AdvaitThale/Solar-MPPT/Final Review/5v-3010-cooling-fan-for-raspberry-pi-550x550.webp

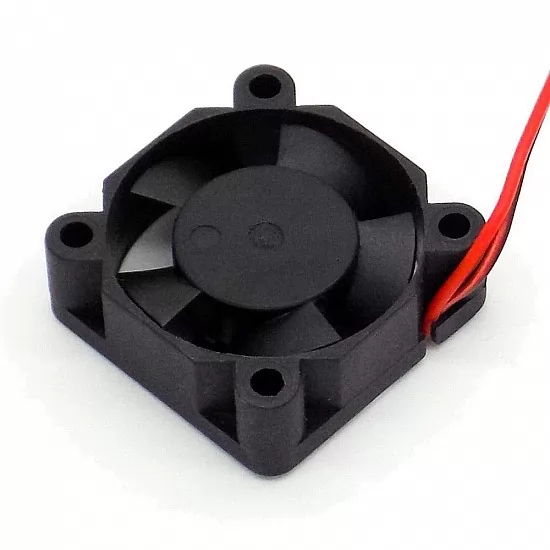
Final Review/5v-3010-cooling-fan-for-raspberry-pi-550x550.webp
