AdvaitThale/Solar-MPPT/Final Review/Back view.png

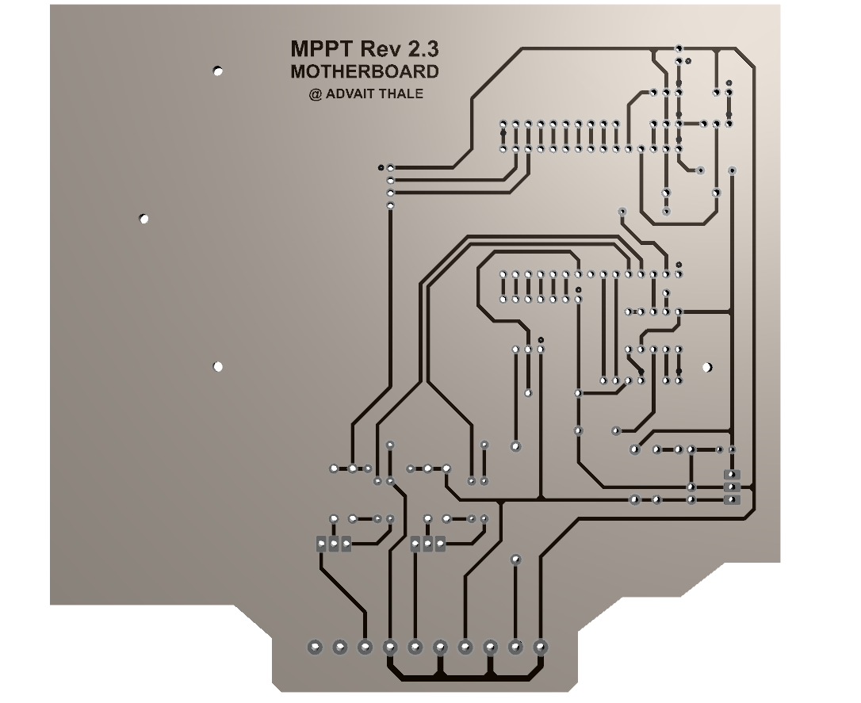
Final Review/Back view.png
