AdvaitThale/Solar-MPPT/Final Review/ESP32-LED-Blink.jpg

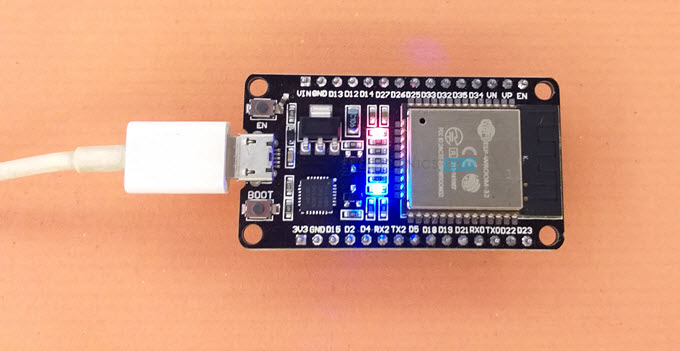
Final Review/ESP32-LED-Blink.jpg
