AdvaitThale/Solar-MPPT/Final Review/inv dau.PNG

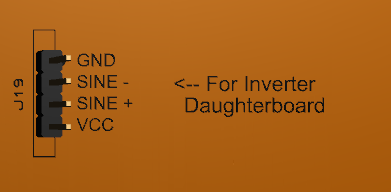
Final Review/inv dau.PNG
