AdvaitThale/Solar-MPPT/Final Review/Main B.PNG

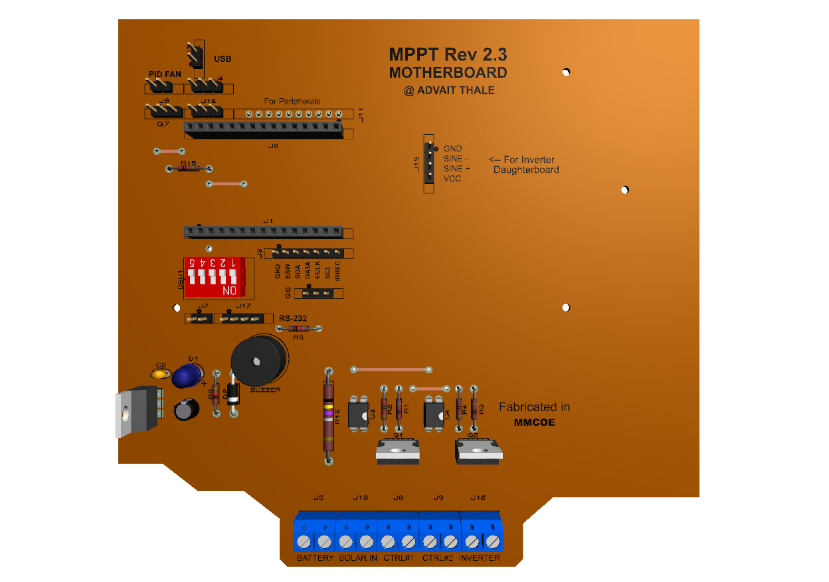
Final Review/Main B.PNG
