AdvaitThale/Solar-MPPT/Review (#1)/Serial Monitor.PNG

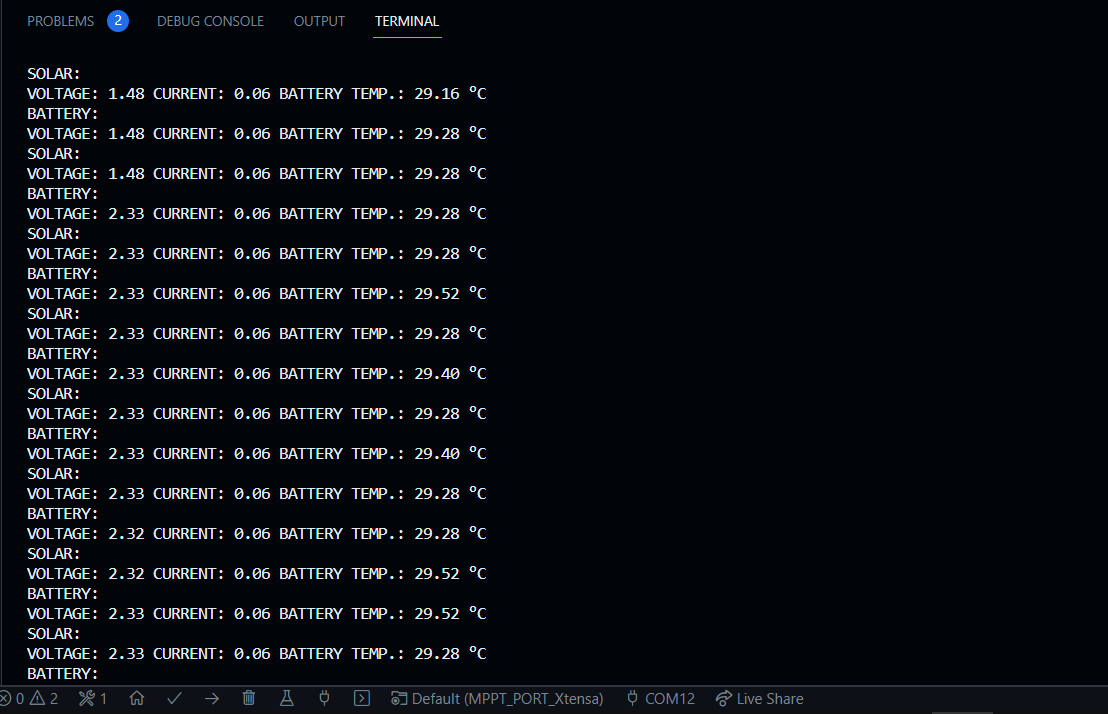
Review (#1)/Serial Monitor.PNG
