AdvaitThale/Solar-MPPT/Review (#1)/WhatsApp Image 2023-05-19 at 08.13.43.jpg

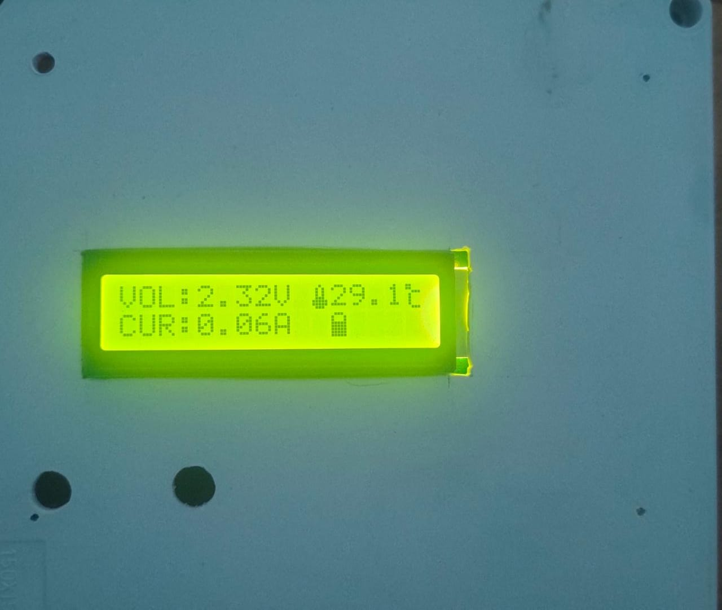
Review (#1)/WhatsApp Image 2023-05-19 at 08.13.43.jpg
